OzKu/humppakuutio/src/Colors.h

#ifndef COLORS_H
#define COLORS_H

#include <Arduino.h>
#include <GraphicsLib.h>

#define COLOR_BG RGB( 15, 15, 15)
#define COLOR_RED RGB(255,  0, 0)
#define COLOR_GREEN RGB(0, 255, 0)
#define COLOR_BLUE RGB(0, 0, 255)
#define COLOR_WHITE RGB(255, 255, 255)
#define COLOR_BUTTON_BG RGB(130, 130, 130)
#define COLOR_BUTTON_PRESSED_BG RGB(110, 110, 110)
#define COLOR_BUTTON_ENABLED RGB(70, 70, 70)

#endif
